causcocharles/Automated_Guided_Vehicle/视觉+驱动+机械臂Arduino_21年工训大赛全国季军开源代码/物料模型和赛道图/2021-工训-Poao/赛道/物流小车赛道-预览.png

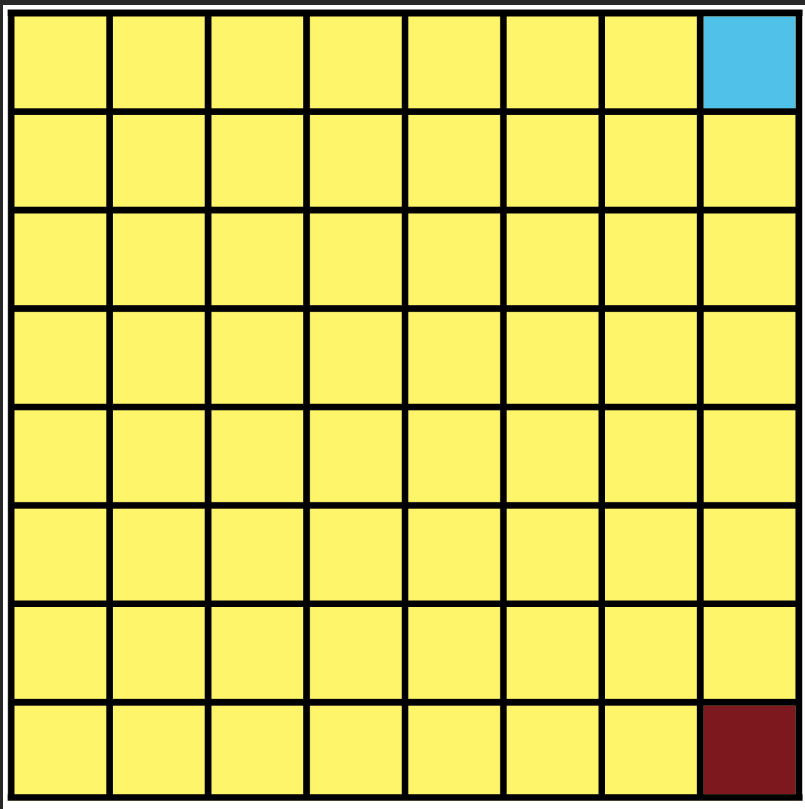
视觉+驱动+机械臂Arduino_21年工训大赛全国季军开源代码/物料模型和赛道图/2021-工训-Poao/赛道/物流小车赛道-预览.png
