causcocharles/Automated_Guided_Vehicle/视觉+驱动+机械臂Arduino_21年工训大赛全国季军开源代码/机械臂+麦轮+步进电机驱动+串口屏显示/MAIN/JXB.ino

// 包含两部分内容：  机械臂抓取顺序计算  ||  机械臂执行动作的判断函数

//  part1 -- 计算顺序    
// void Compute_xj();

inline int Compute(char* str1, char* str2)  // 解算 str1 in str2 的顺序  -- 基本函数
{    // 返回整型的顺序  
//   Serial.println(F("jxxxxx"));
  int sum = 0;
   for(int i=0; i<3;i++)
  {
    char cc = str1[i];
    char* xx = strchr(str2, cc);    // 搜寻cc在str2中顺序
    int pos = xx - str2 +1;         // 取得所需顺序 1、2、3...
    sum = sum*10 + pos;             // 计算顺序对应的整型数值
    }
    return sum;                     // 返回值
  }
  
//   计算相关顺序： SS1_order、SS2_order、XX1_order、XX2_order
inline  void Compute_xj()     // 直接调用
{
//  Serial.println(F("Ready for xj"));
 Serial.println(F("Ready for xj"));
  // 1、将 string 转换为 char*      【char* xx = string.c_str();】  
//  char* SeHuan = SeH_pose.c_str();     // 色环顺序
  char* WL1 = WL1_pose.c_str();        // 上层物料顺序
  char* WL2 = WL2_pose.c_str();        // 下层物料顺序
  char* QR1 = QR1_code.c_str();        // 任务码1顺序
  char* QR2 = QR2_code.c_str();        // 任务码2顺序
  
  // 2、解算顺序，并保存为String
  int aa = Compute(QR1,WL1);
  int bb = Compute(QR1,SeHuan);

  int cc = Compute(QR2,WL2);
  int dd = Compute(QR2,SeHuan);

// 这里为何如此简单粗暴？ 请前文系列文章找答案 —— 当时被逼无奈
   A[0]= aa/100+'0';   // 123/100 = 1
   A[1]= aa/10%10+'0';   // 123/10%10 = 2
   A[2]= aa%10+'0';   // 123%10 = 3
   A[3] ='\0';
   B[0]= bb/100+'0';   // 123/100 = 1
   B[1]= bb/10%10+'0';   // 123/10%10 = 2
   B[2]= bb%10+'0';   // 123%10 = 3
   B[3] ='\0';
   C[0]= cc/100+'0';   // 123/100 = 1
   C[1]= cc/10%10+'0';   // 123/10%10 = 2
   C[2]= cc%10+'0';   // 123%10 = 3
   C[3] ='\0';
   D[0]= dd/100+'0';   // 123/100 = 1
   D[1]= dd/10%10+'0';   // 123/10%10 = 2
   D[2]= dd%10+'0';   // 123%10 = 3
   D[3] ='\0';

  Serial.print(F("SS2_order: "));
  Serial.println(A);  Serial.println(aa);
  Serial.print(F("SS2_order: "));
  Serial.println(B);Serial.println(bb);
  Serial.print(F("XX1_order: "));
  Serial.print(C);Serial.println(cc);
  Serial.print(F("XX2_order: "));
  Serial.println(D);Serial.println(dd);
  
//  Serial.println("XX1_order: "+ cc + "     XX2_order: "+ dd);
  }


// part2 -- 机械臂抓取动作
// QR_shibie();
// Shibie_Wuliao();
//  动作组 3 + 3 +3 +3 +3 +3 +3（抓取放置动作值 21）     + 1+1  （扫描二维码+识别物料动作值 2）
//  void Shangceng_Yuanliaoqu_Zhua(String inString);               // 抓取上层物料
//  void Xiaceng_Yuanliaoqu_Zhua(String inString);                 // 抓取下层物料
//  void Fangdao_Cujiagongqu(String inString);                     // 放置到粗加工区
//  void Cujiagongqu_Zhuaqu(String inString);                      // 从粗加工区抓取
//  void Fangdao_Banchengpinqu_Shangceng(String inString);         // 上层物料放到半成品区
//  void Fangdao_Banchengpinqu_Xiaceng(String inString);           // 下层物料放到半成品区
/*
 SMQ          扫描二维码前  SMQ--扫描前 首拼
 KWL          识别物料顺序前  KWL--看物料 首拼
 FWH          识别物料顺序后，复位状态  FWH--复位后 首拼
 YLS_123_321  原料区上层物料抓取
 YLX_123_321  原料区上层物料抓取
 JGQ_123_321  粗加工区抓取物料放到小车上
 JGF_123_321  粗加工区物料放到色环
 BCS_123_321  半成品区上层物料抓取
 BCX_123_321  半成品区下层物料抓取
 */
 void QR_shibie(){
    
            myse.runActionGroup(22,1);  //第22组为识别二维码
  
     recv_OK(); // 完成动作后的反馈 
//      recv_OK(); // 完成动作后的反馈 
}
 void QR_shibiehao(){
    
            myse.runActionGroup(23,1);  //第23组为识别二维码
  
     recv_OK(); // 完成动作后的反馈 
      recv_OK(); // 完成动作后的反馈 
}
 void Shibie_Wuliao(){
    
            myse.runActionGroup(24,1);  //第24组为识别物料状态
      
       recv_OK(); // 完成动作后的反馈 
        recv_OK(); // 完成动作后的反馈 
}
void Shibie_WuliaoHou(){
    
            myse.runActionGroup(25,1);  //第25组为识别物料完成后，复位状态
      
       recv_OK(); // 完成动作后的反馈 
//       recv_OK(); // 完成动作后的反馈 
}


inline void Shangceng_Yuanliaoqu_Zhua(){     //函数名为  上层 原料 抓  原料区上层物料抓取
     Serial.println(F("Ready for YLS"));
     if(A[0]=='1' &&A[1]=='2' &&A[2]=='3' )
     {
      myse.runActionGroup(1,1);  //运行1号动作组
            recv_OK(); // 完成动作后的反馈 
            recv_OK(); // 完成动作后的反馈
       Fangdao_Chuwucao(0,0);       
      myse.runActionGroup(2,1);  //运行1号动作组
            recv_OK(); // 完成动作后的反馈 
            recv_OK(); // 完成动作后的反馈
       Fangdao_Chuwucao(1,0); 
      myse.runActionGroup(3,1);  //运行1号动作组
            recv_OK(); // 完成动作后的反馈 
            recv_OK(); // 完成动作后的反馈
       Fangdao_Chuwucao(2,0);    
      }
     else  if(A[0]=='1' &&A[1]=='3' &&A[2]=='2' )
     {
      myse.runActionGroup(1,1);  //运行1号动作组
            recv_OK(); // 完成动作后的反馈 
            recv_OK(); // 完成动作后的反馈
       Fangdao_Chuwucao(0,0);       
      myse.runActionGroup(3,1);  //运行1号动作组
            recv_OK(); // 完成动作后的反馈 
            recv_OK(); // 完成动作后的反馈
       Fangdao_Chuwucao(1,0); 
      myse.runActionGroup(2,1);  //运行1号动作组
            recv_OK(); // 完成动作后的反馈 
            recv_OK(); // 完成动作后的反馈
       Fangdao_Chuwucao(2,0);    
      }
      else if(A[0]=='2' &&A[1]=='3' &&A[2]=='1' )
     {
      myse.runActionGroup(2,1);  //运行1号动作组
            recv_OK(); // 完成动作后的反馈 
            recv_OK(); // 完成动作后的反馈
       Fangdao_Chuwucao(0,0);       
      myse.runActionGroup(3,1);  //运行1号动作组
            recv_OK(); // 完成动作后的反馈 
            recv_OK(); // 完成动作后的反馈
       Fangdao_Chuwucao(1,0); 
      myse.runActionGroup(1,1);  //运行1号动作组
            recv_OK(); // 完成动作后的反馈 
            recv_OK(); // 完成动作后的反馈
       Fangdao_Chuwucao(2,0);    
      }
      else  if(A[0]=='2' &&A[1]=='1' &&A[2]=='3' )
     {
      myse.runActionGroup(2,1);  //运行1号动作组
            recv_OK(); // 完成动作后的反馈 
            recv_OK(); // 完成动作后的反馈
       Fangdao_Chuwucao(0,0);       
      myse.runActionGroup(1,1);  //运行1号动作组
            recv_OK(); // 完成动作后的反馈 
            recv_OK(); // 完成动作后的反馈
       Fangdao_Chuwucao(1,0); 
      myse.runActionGroup(3,1);  //运行1号动作组
            recv_OK(); // 完成动作后的反馈 
            recv_OK(); // 完成动作后的反馈
       Fangdao_Chuwucao(2,0);    
      }
      else  if(A[0]=='3' &&A[1]=='1' &&A[2]=='2' )
     {
      myse.runActionGroup(3,1);  //运行1号动作组
            recv_OK(); // 完成动作后的反馈 
            recv_OK(); // 完成动作后的反馈
       Fangdao_Chuwucao(0,0);       
      myse.runActionGroup(1,1);  //运行1号动作组
            recv_OK(); // 完成动作后的反馈 
            recv_OK(); // 完成动作后的反馈
       Fangdao_Chuwucao(1,0); 
      myse.runActionGroup(2,1);  //运行1号动作组
            recv_OK(); // 完成动作后的反馈 
            recv_OK(); // 完成动作后的反馈
       Fangdao_Chuwucao(2,0);    
      }
      else  if(A[0]=='3' &&A[1]=='2' &&A[2]=='1' )
     {
      myse.runActionGroup(3,1);  //运行1号动作组
            recv_OK(); // 完成动作后的反馈 
            recv_OK(); // 完成动作后的反馈
       Fangdao_Chuwucao(0,0);       
      myse.runActionGroup(2,1);  //运行1号动作组
            recv_OK(); // 完成动作后的反馈 
            recv_OK(); // 完成动作后的反馈
       Fangdao_Chuwucao(1,0); 
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
            recv_OK(); // 完成动作后的反馈
      myse.runActionGroup(20,1);  //运行1号动作组
            recv_OK(); // 完成动作后的反馈 
            recv_OK(); // 完成动作后的反馈
      myse.runActionGroup(19,1);  //运行1号动作组
            recv_OK(); // 完成动作后的反馈 
            recv_OK(); // 完成动作后的反馈
      }
      
     
}
